elizabetabudini/iot-smart-green-house/src/sgh-edge/sgh-edge/Potenziometro.h

#ifndef __POTENZIOMETRO__
#define __POTENZIOMETRO__
#include "Arduino.h"

/**
 * Class used to manage the potentiometer, used to detect the sugar level.
 */
class Potenziometro {
  public:
    Potenziometro(String pin);
    int getValue();
  protected:
    String pin;
};

#endif
